daglem/reDIP-SX/hardware/reDIP-SX.sch

## KiCad design hardware/reDIP-SX.sch (2021-05-01)

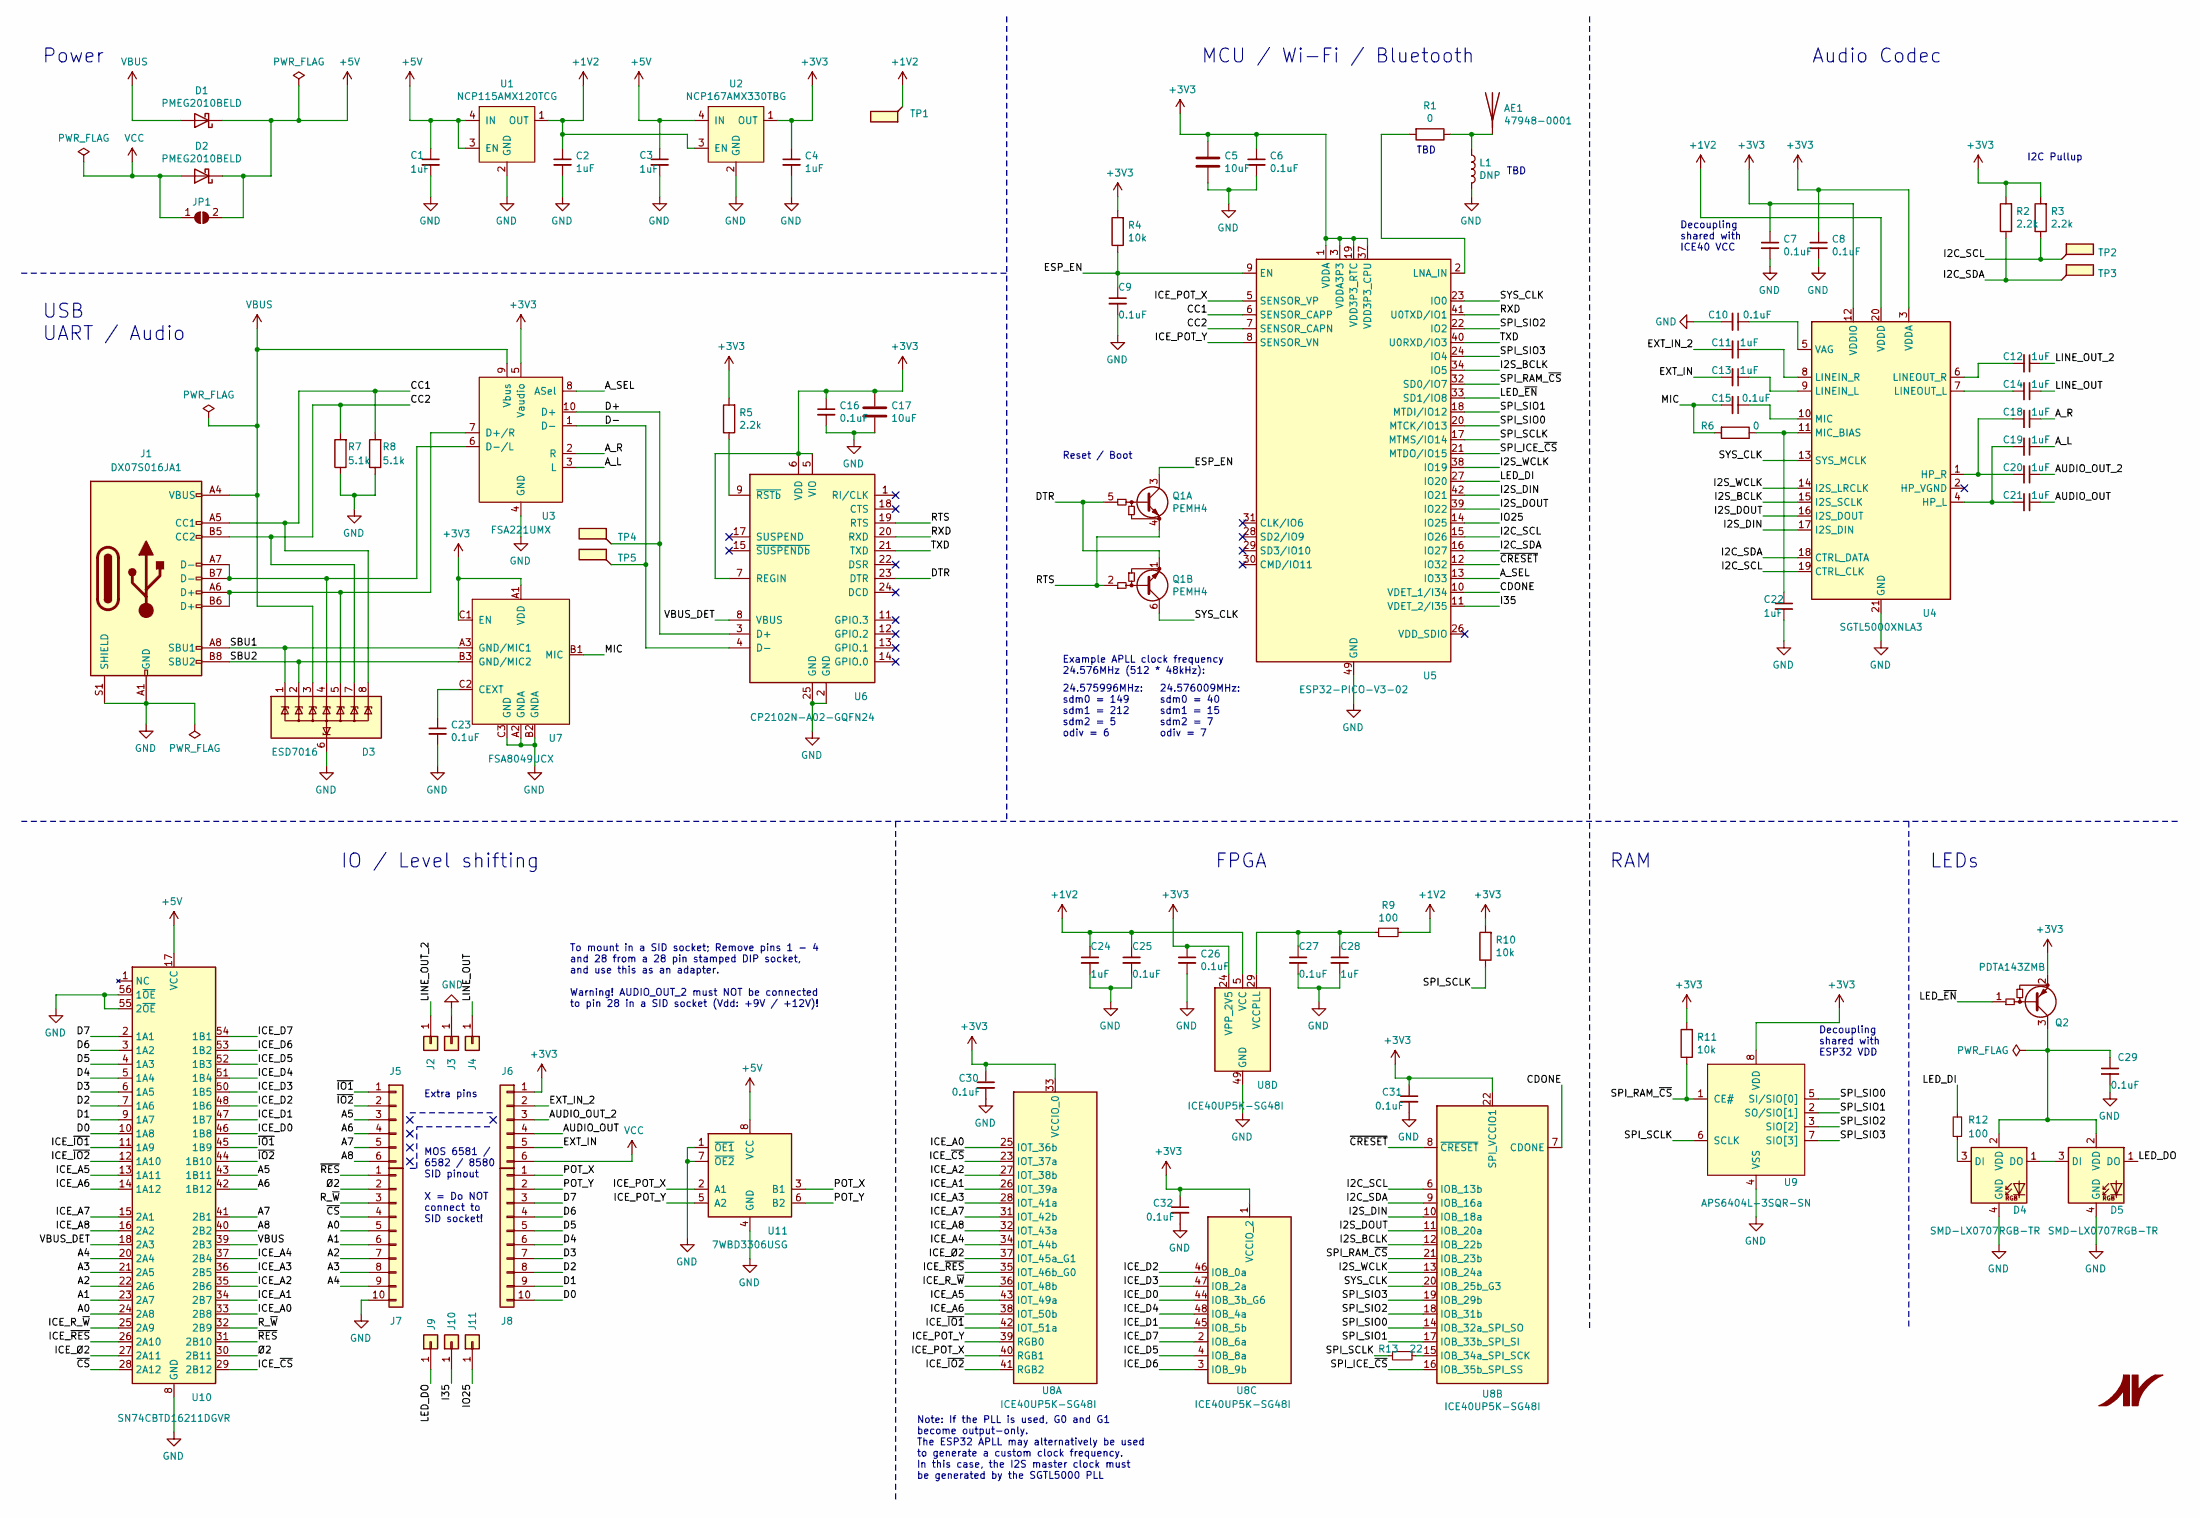
[picture p20: schematic reDIP-SX.sch]

Parts:
AE1: 47948-0001; Molex_47948-0001
C1, C3: 1uF; C_0402_1005Metric
C2, C4, C11, C12, C13, C14, C18, C19, C20, C21, C22, C24, C28: 1uF; C_0201_0603Metric
C5, C17: 10uF; C_0402_1005Metric
C6, C7, C8, C9, C10, C15, C16, C23, C25, C26, C27, C29, C30, C31, C32: 0.1uF; C_0201_0603Metric
D1, D2: PMEG2010BELD; D_SOD-882D
D3: ESD7016; 517CB-3.3x1.0mm_P0.4mm
D4, D5: SMD-LX0707RGB-TR
J1: DX07S016JA1; USB_C_Receptacle_JAE_DX07S016JA1
J2, J3, J4, J10, J11: Conn_01x01; SolderWirePad_1x01_SMD_1.5x3mm
J5, J6: Conn_01x06; PinHeader_1x06_P2.54mm_Vertical_LongTail
J7, J8: Conn_01x10; PinHeader_1x10_P2.54mm_Vertical
J9: Conn_01x01; SolderWirePad_1x01_SMD_1x2mm
JP1: SolderJumper_2_Open; DNP_0402_1005Metric
L1: DNP; DNP_0201_0603Metric
Q1: PEMH4; SOT-666
Q2: PDTA143ZMB; SOT-883
R1, R6: 0; R_0201_0603Metric
R2, R3, R5: 2.2k; R_0201_0603Metric
R4, R10, R11: 10k; R_0201_0603Metric
R7, R8: 5.1k; R_0201_0603Metric
R9, R12: 100; R_0201_0603Metric
R13: 22; R_0201_0603Metric
TP1, TP2, TP3, TP4, TP5: TestPoint_Flag; TestPoint_Pad_D0.75mm
U1: NCP115AMX120TCG; CASE_711AJ_1.0x1.0mm_P0.65mm
U2: NCP167AMX330TBG; CASE_711AJ_1.0x1.0mm_P0.65mm
U3: FSA221UMX; CASE_523BC_1.4x1.8_P0.4mm
U4: SGTL5000XNLA3; QFN-20-1EP_3x3mm_P0.4mm_EP1.65x1.65mm
U5: ESP32-PICO-V3-02; QFN-48-1EP_7x7mm_P0.5mm_EP5.3x5.3mm
U6: CP2102N-A02-GQFN24; QFN-24-1EP_4x4mm_P0.5mm_EP2.6x2.6mm
U7: FSA8049UCX; WLCSP-9_1.16x1.16mm_Layout3x3_P0.4mm
U8: ICE40UP5K-SG48I; QFN-48-1EP_7x7mm_P0.5mm_EP5.6x5.6mm
U9: APS6404L-3SQR-SN; SOP-8_3.9x4.9mm_P1.27mm
U10: SN74CBTD16211DGVR; Texas_TVSOP-56_4.4x11.3mm_P0.4mm
U11: 7WBD3306USG; CASE_493-8_2.3x2mm_P0.5mm

Connections:
+1V2: C2.1, C24.1, C25.1, R9.1, TP1.1, U1.1 (OUT), U2.3 (EN), U4.20 (VDDD), U8.5 (VCC), U8.30 (VCC)
+3V3: C4.1, C5.1, C6.1, C7.1, C8.1, C16.1, C17.1, C26.1, C30.1, C31.1, C32.1, J6.1, Q2.2 (E), R2.2, R3.2, R4.2, R5.2, R10.2, R11.2, U2.1 (OUT), U3.5 (Vaudio), U4.3 (VDDA), U4.12 (VDDIO), U5.1 (VDDA), U5.3 (VDDA3P3), U5.4 (VDDA3P3), U5.19 (VDD3P3_RTC), U5.37 (VDD3P3_CPU), U5.43 (VDDA), U5.46 (VDDA), U6.5 (VIO), U6.6 (VDD), U6.7 (REGIN), U7.A1 (VDD), U7.C1 (EN), U8.1 (VCCIO_2), U8.22 (SPI_VCCIO1), U8.24 (VPP_2V5), U8.33 (VCCIO_0), U9.8 (VDD)
+5V: C1.1, C3.1, D1.1 (K), D2.1 (K), JP1.2 (B), U1.3 (EN), U1.4 (IN), U2.4 (IN), U10.17 (VCC), U11.8 (VCC)
A0: J7.5, U10.24 (2A8)
A1: J7.6, U10.23 (2A7)
A2: J7.7, U10.22 (2A6)
A3: J7.8, U10.21 (2A5)
A4: J7.9, U10.20 (2A4)
A5: J5.3, U10.43 (1B11)
A6: J5.4, U10.42 (1B12)
A7: J5.5, U10.41 (2B1)
A8: J5.6, U10.40 (2B2)
AUDIO_OUT: C21.1, J6.4
AUDIO_OUT_2: C20.1, J6.3
A_L: C19.1, U3.3 (L)
A_R: C18.1, U3.2 (R)
A_SEL: U3.8 (ASel), U5.13 (IO33)
CC1: D3.8 (IO6), J1.A5 (CC1), R8.2, U5.6 (SENSOR_CAPP)
CC2: D3.7 (IO5), J1.B5 (CC2), R7.2, U5.7 (SENSOR_CAPN)
CDONE: U5.10 (VDET_1/I34), U8.7 (CDONE)
D0: J8.10, U10.10 (1A8)
D1: J8.9, U10.9 (1A7)
D2: J8.8, U10.7 (1A6)
D3: J8.7, U10.6 (1A5)
D4: J8.6, U10.5 (1A4)
D5: J8.5, U10.4 (1A3)
D6: J8.4, U10.3 (1A2)
D7: J8.3, U10.2 (1A1)
D+: TP4.1, U3.10 (D+), U6.3 (D+)
D-: TP5.1, U3.1 (D-), U6.4 (D-)
DTR: Q1.1 (E1), Q1.5 (B1), U6.23 (DTR)
ESP_EN: C9.1, Q1.3 (C1), R4.1, U5.9 (EN)
EXT_IN: C13.2, J6.5
EXT_IN_2: C11.2, J6.2
GND: C1.2, C2.2, C3.2, C4.2, C5.2, C6.2, C7.2, C8.2, C9.2, C10.2, C16.2, C17.2, C22.2, C23.2, C24.2, C25.2, C26.2, C27.2, C28.2, C29.2, C30.2, C31.2, C32.2, D3.6 (GND), D3.9 (GND), D4.4 (GND), D5.4 (GND), J1.A1 (GND), J1.A12 (GND), J1.B1 (GND), J1.B12 (GND), J1.S1 (SHIELD), J3.1, J7.10, L1.2, R7.1, R8.1, U1.2 (GND), U2.2 (GND), U3.4 (GND), U4.21 (GND), U5.49 (GND), U6.2 (GND), U6.25 (GND), U7.A2 (GNDA), U7.B2 (GNDA), U7.C3 (GND), U8.49 (GND), U9.4 (VSS), U10.8 (GND), U10.19 (GND), U10.38 (GND), U10.49 (GND), U10.55 (2~OE~), U10.56 (1~OE~), U11.1 (~OE1~), U11.4 (GND), U11.7 (~OE2~)
I2C_SCL: R3.1, TP2.1, U4.19 (CTRL_CLK), U5.15 (IO26), U8.6 (IOB_13b)
I2C_SDA: R2.1, TP3.1, U4.18 (CTRL_DATA), U5.16 (IO27), U8.9 (IOB_16a)
I2S_BCLK: U4.15 (I2S_SCLK), U5.34 (IO5), U8.12 (IOB_22b)
I2S_DIN: U4.17 (I2S_DIN), U5.42 (IO21), U8.10 (IOB_18a)
I2S_DOUT: U4.16 (I2S_DOUT), U5.39 (IO22), U8.11 (IOB_20a)
I2S_WCLK: U4.14 (I2S_LRCLK), U5.38 (IO19), U8.13 (IOB_24a)
I35: J10.1, U5.11 (VDET_2/I35)
ICE_A0: U8.25 (IOT_36b), U10.33 (2B8)
ICE_A1: U8.26 (IOT_39a), U10.34 (2B7)
ICE_A2: U8.27 (IOT_38b), U10.35 (2B6)
ICE_A3: U8.28 (IOT_41a), U10.36 (2B5)
ICE_A4: U8.34 (IOT_44b), U10.37 (2B4)
ICE_A5: U8.43 (IOT_49a), U10.13 (1A11)
ICE_A6: U8.38 (IOT_50b), U10.14 (1A12)
ICE_A7: U8.31 (IOT_42b), U10.15 (2A1)
ICE_A8: U8.32 (IOT_43a), U10.16 (2A2)
ICE_D0: U8.44 (IOB_3b_G6), U10.46 (1B8)
ICE_D1: U8.45 (IOB_5b), U10.47 (1B7)
ICE_D2: U8.46 (IOB_0a), U10.48 (1B6)
ICE_D3: U8.47 (IOB_2a), U10.50 (1B5)
ICE_D4: U8.48 (IOB_4a), U10.51 (1B4)
ICE_D5: U8.4 (IOB_8a), U10.52 (1B3)
ICE_D6: U8.3 (IOB_9b), U10.53 (1B2)
ICE_D7: U8.2 (IOB_6a), U10.54 (1B1)
ICE_POT_X: U5.5 (SENSOR_VP), U8.40 (RGB1), U11.2 (A1)
ICE_POT_Y: U5.8 (SENSOR_VN), U8.39 (RGB0), U11.5 (A2)
ICE_R_~W~: U8.36 (IOT_48b), U10.25 (2A9)
ICE_~CS~: U8.23 (IOT_37a), U10.29 (2B12)
ICE_~IO1~: U8.42 (IOT_51a), U10.11 (1A9)
ICE_~IO2~: U8.41 (RGB2), U10.12 (1A10)
ICE_~RES~: U8.35 (IOT_46b_G0), U10.26 (2A10)
ICE_Ø2: U8.37 (IOT_45a_G1), U10.27 (2A11)
IO25: J11.1, U5.14 (IO25)
LED_DI: R12.2, U5.27 (IO20)
LED_DO: D5.1 (DO), J9.1
LED_~EN~: Q2.1 (B), U5.33 (SD1/IO8)
LINE_OUT: C14.1, J4.1
LINE_OUT_2: C12.1, J2.1
MIC: C15.2, R6.2, U7.B1 (MIC)
unnamed: AE1.1, L1.1, R1.1
unnamed: C10.1, U4.5 (VAG)
unnamed: C11.1, U4.8 (LINEIN_R)
unnamed: C12.2, U4.6 (LINEOUT_R)
unnamed: C13.1, U4.9 (LINEIN_L)
unnamed: C14.2, U4.7 (LINEOUT_L)
unnamed: C15.1, U4.10 (MIC)
unnamed: C18.2, C20.2, U4.1 (HP_R)
unnamed: C19.2, C21.2, U4.4 (HP_L)
unnamed: C22.1, R6.1, U4.11 (MIC_BIAS)
unnamed: C23.1, U7.C2 (CEXT)
unnamed: C27.1, C28.1, R9.2, U8.29 (VCCPLL)
unnamed: C29.1, D4.2 (VDD), D5.2 (VDD), Q2.3 (C)
unnamed: D3.4 (IO3), J1.A7 (D-), J1.B7 (D-), U3.6 (D-/L)
unnamed: D3.5 (IO4), J1.A6 (D+), J1.B6 (D+), U3.7 (D+/R)
unnamed: D4.1 (DO), D5.3 (DI)
unnamed: D4.3 (DI), R12.1
unnamed: R1.2, U5.2 (LNA_IN)
unnamed: R5.1, U6.9 (~RSTb)
unnamed: R13.1, U8.15 (IOB_34a_SPI_SCK)
POT_X: J8.1, U11.3 (B1)
POT_Y: J8.2, U11.6 (B2)
RTS: Q1.2 (B1), Q1.4 (E1), U6.19 (RTS)
RXD: U5.41 (U0TXD/IO1), U6.20 (RXD)
R_~W~: J7.3, U10.32 (2B9)
SBU1: D3.1 (IO1), J1.A8 (SBU1), U7.A3 (GND/MIC1)
SBU2: D3.2 (IO2), J1.B8 (SBU2), U7.B3 (GND/MIC2)
SPI_ICE_~CS~: U5.21 (MTDO/IO15), U8.16 (IOB_35b_SPI_SS)
SPI_RAM_~CS~: R11.1, U5.32 (SD0/IO7), U8.21 (IOB_23b), U9.1 (CE#)
SPI_SCLK: R10.1, R13.2, U5.17 (MTMS/IO14), U9.6 (SCLK)
SPI_SIO0: U5.20 (MTCK/IO13), U8.14 (IOB_32a_SPI_SO), U9.5 (SI/SIO[0])
SPI_SIO1: U5.18 (MTDI/IO12), U8.17 (IOB_33b_SPI_SI), U9.2 (SO/SIO[1])
SPI_SIO2: U5.22 (IO2), U8.18 (IOB_31b), U9.3 (SIO[2])
SPI_SIO3: U5.24 (IO4), U8.19 (IOB_29b), U9.7 (SIO[3])
SYS_CLK: Q1.6 (C1), U4.13 (SYS_MCLK), U5.23 (IO0), U8.20 (IOB_25b_G3)
TXD: U5.40 (U0RXD/IO3), U6.21 (TXD)
VBUS: D1.2 (A), D3.3 (VBUS), D3.10 (VBUS), J1.A4 (VBUS), J1.A9 (VBUS), J1.B4 (VBUS), J1.B9 (VBUS), U3.9 (Vbus), U10.39 (2B3)
VBUS_DET: U6.8 (VBUS), U10.18 (2A3)
VCC: D2.2 (A), J6.6, JP1.1 (A)
~CRESET~: U5.12 (IO32), U8.8 (~CRESET)
~CS~: J7.4, U10.28 (2A12)
~IO1~: J5.1, U10.45 (1B9)
~IO2~: J5.2, U10.44 (1B10)
~RES~: J7.1, U10.31 (2B10)
Ø2: J7.2, U10.30 (2B11)

Notes on the sheet:
USB UART / Audio
LEDs
RAM
FPGA
IO / Level shifting
I2C Pullup
Decoupling shared with ICE40 VCC
Audio Codec
MCU / Wi-Fi / Bluetooth
Power
Decoupling shared with ESP32 VDD
Reset / Boot
TBD
Extra pins
To mount in a SID socket; Remove pins 1 - 4 and 28 from a 28 pin stamped DIP socket, and use this as an adapter. Warning! AUDIO_OUT_2 must NOT be connected to pin 28 in a SID socket (Vdd: +9V / +12V)!
MOS 6581 / 6582 / 8580 SID pinout X = Do NOT connect to SID socket!
Example APLL clock frequency 24.576MHz (512 * 48kHz):
24.575996MHz: sdm0 = 149 sdm1 = 212 sdm2 = 5 odiv = 6
24.576009MHz: sdm0 = 40 sdm1 = 15 sdm2 = 7 odiv = 7
Note: If the PLL is used, G0 and G1 become output-only. The ESP32 APLL may alternatively be used to generate a custom clock frequency. In this case, the I2S master clock must be generated by the SGTL5000 PLL
